Ptakoninja/Zasilacz-stabilizowany-bez-LM317/Projekt.asc

C1: polcap; 1000µ; V=25 Irms=2.88 Rser=0.0117 Lser=9.49n
C2: polcap; 2.2µ; V=25 Irms=2.88 Rser=0.0117 Lser=9.49n
C3: cap; 100n
C4: cap; 100n
C5: cap; 10n
C6: cap; 10n
C7: cap; 47n
D5: zener; 1N750
D6: schottky; RBR20T60ANZ
D7: schottky; RBE2VAM20A
Q1: npn; 2SD2673
Q2: npn; 2SD2673
R1: res; 7.5k
R2: res; 10k
R3: res; 110k
R4: res; 4.7k
R5: res; 120k
R6: res; 4,7k
R7: res; 2.2k
R8: res; 10k
R9: res; 2.2k
R10: res; 10k
R11: res; 1k
R12: res; 2k
R13: res; 3k
R14: res; 2.5k
R15: res; 2.5k
R16: res; 0.1
U3: OP77
U4: OP77
V1: voltage; 15
Named nets: 0, 5V, KKK
.tran 1
